bujna94/MoonClock/MOONCLOCK/secrets.py

# This file is where you keep secret settings, passwords, and tokens!
# If you put them in the code you risk committing that info or sharing it

secrets = [
    {
        'ssid': 'WIFI_SSID',
        'password': 'WIFI_PASSWORD',
    },
    # {
    #    'ssid': 'WIFI_SSID2',
    #    'password': 'WIFI_PASSWORD2',
    # },
    # {
    #    'ssid': 'WIFI_SSID3',
    #    'password': 'WIFI_PASSWORD3',
    # },
]
